Rezzonics/SuperFuzzWah/Simulation/FuzzWah_LTSpice_sch.jpg

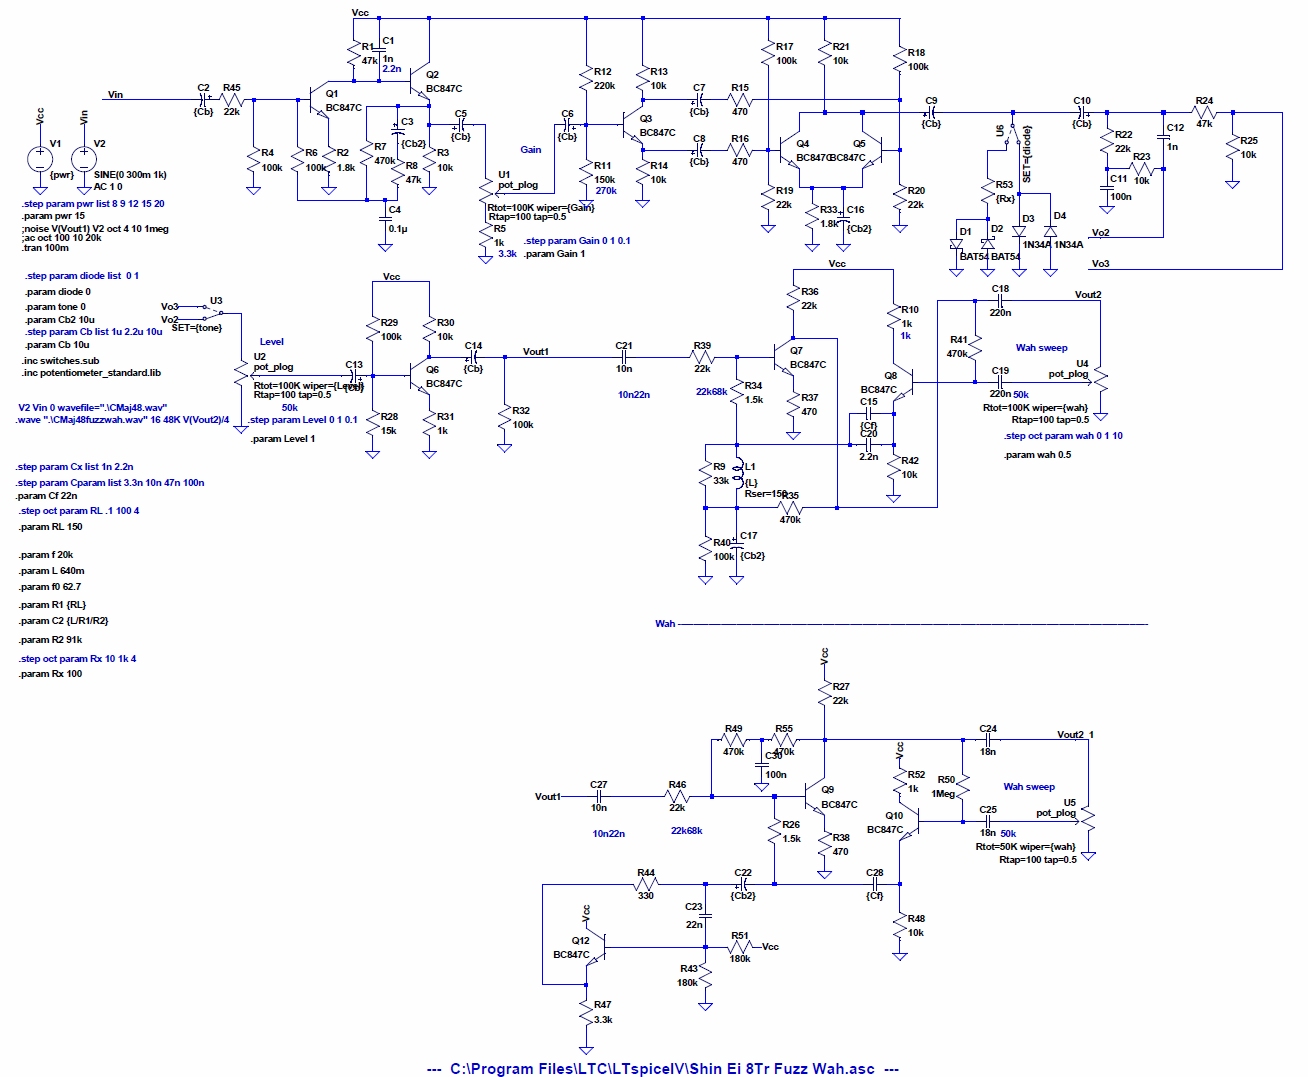
Simulation/FuzzWah_LTSpice_sch.jpg
