Rezzonics/SuperFuzzWah/Simulation/FuzzWah_LTSpice_V2.jpg

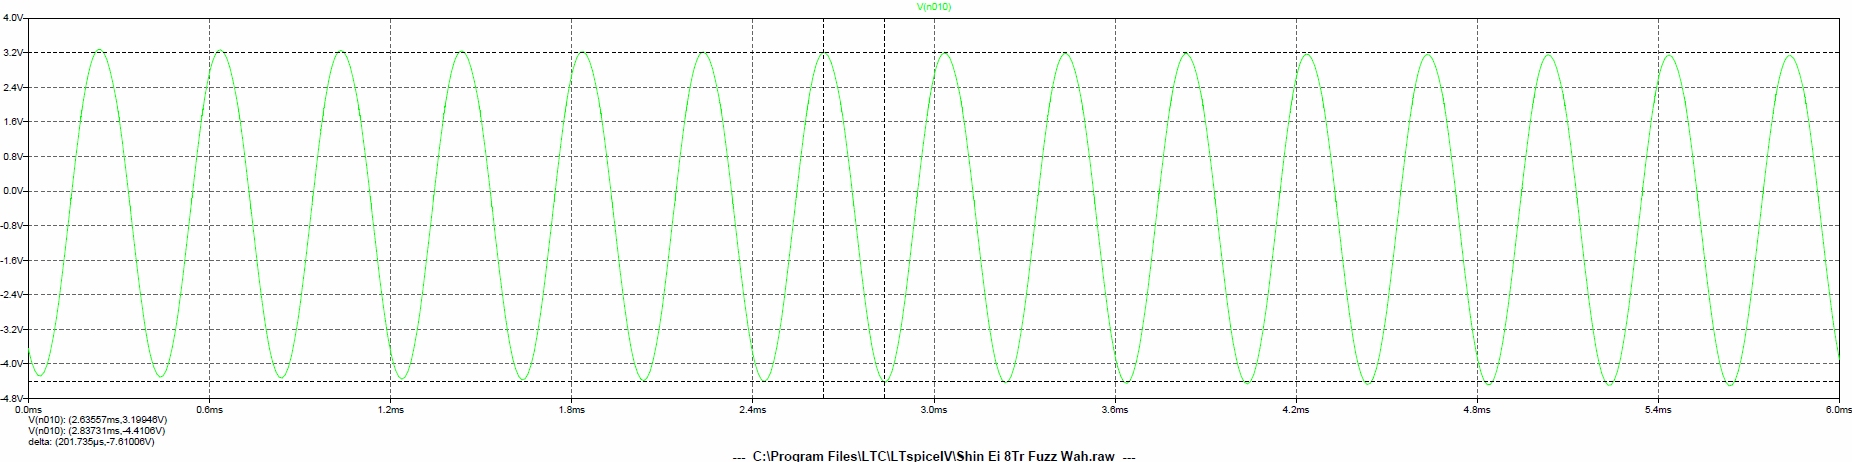
Simulation/FuzzWah_LTSpice_V2.jpg
