Rezzonics/SuperFuzzWah/Simulation/FuzzWah_LTSpice_V3.jpg

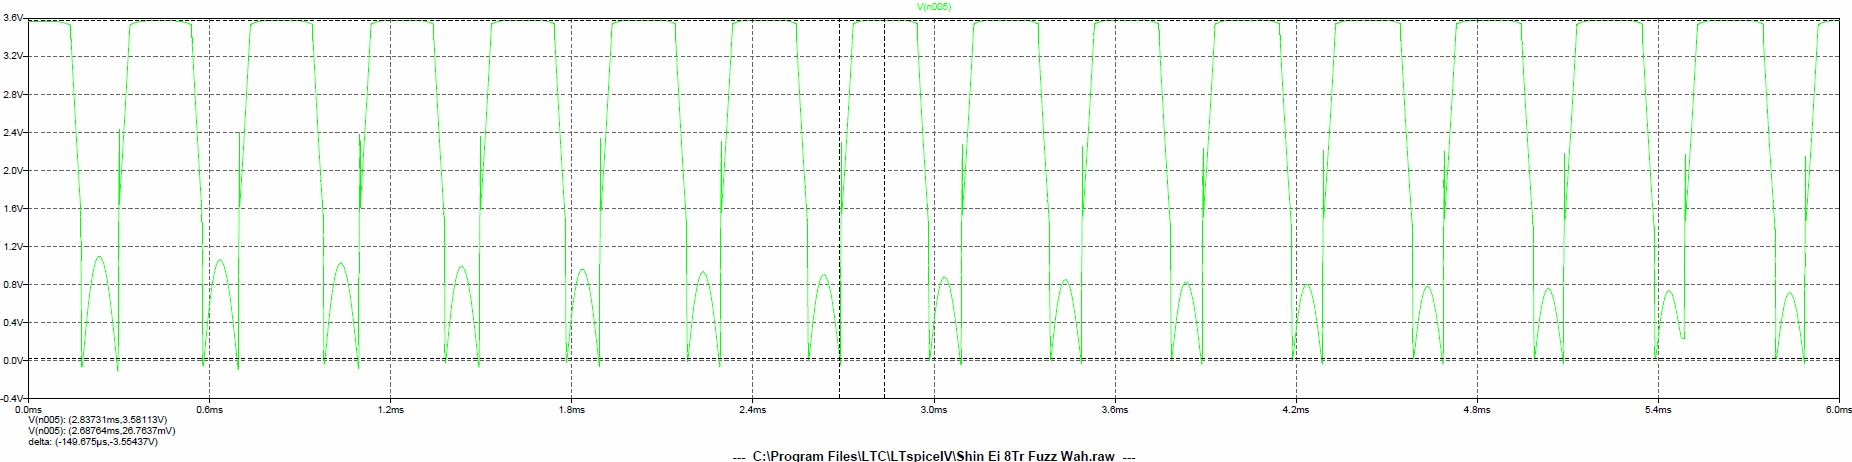
Simulation/FuzzWah_LTSpice_V3.jpg
