Rezzonics/SuperFuzzWah/Simulation/FuzzWah_LTSpice_V4.jpg

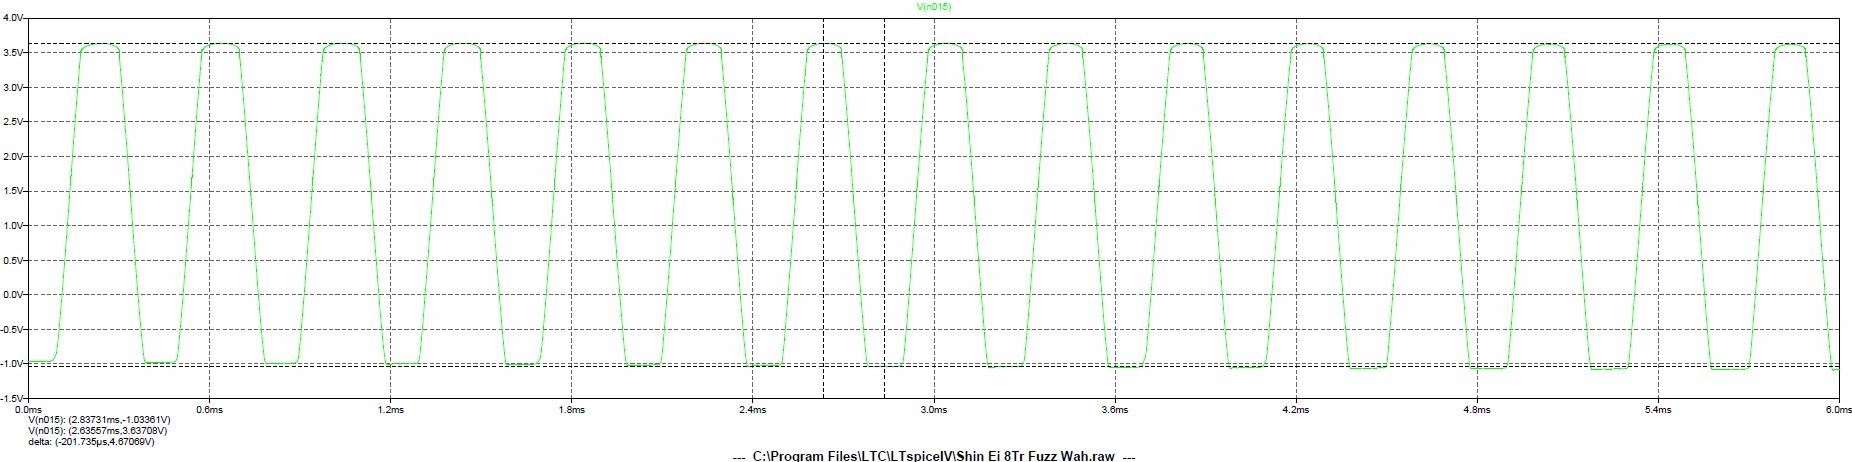
Simulation/FuzzWah_LTSpice_V4.jpg
