Rezzonics/SuperFuzzWah/Simulation/FuzzWah_LTSpice_V5.jpg

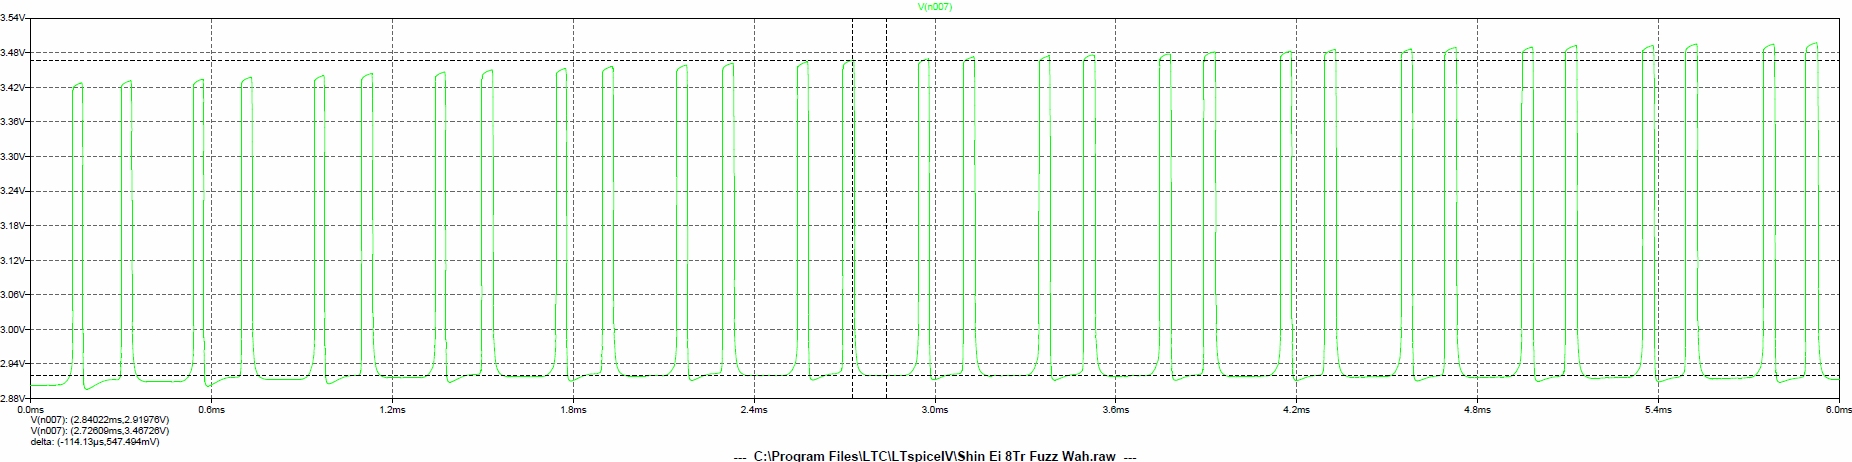
Simulation/FuzzWah_LTSpice_V5.jpg
