Rezzonics/SuperFuzzWah/Simulation/FuzzWah_LTSpice_V8.jpg

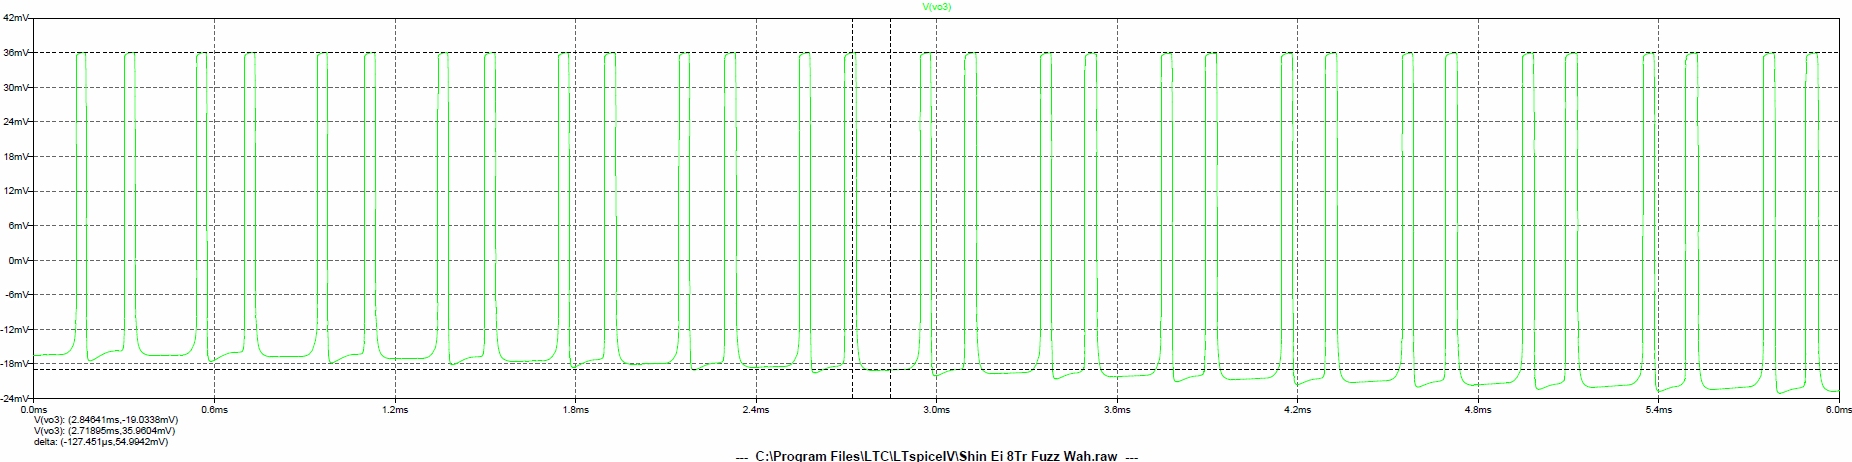
Simulation/FuzzWah_LTSpice_V8.jpg
