Rezzonics/SuperFuzzWah/Simulation/FuzzWah_LTSpice_V9.jpg

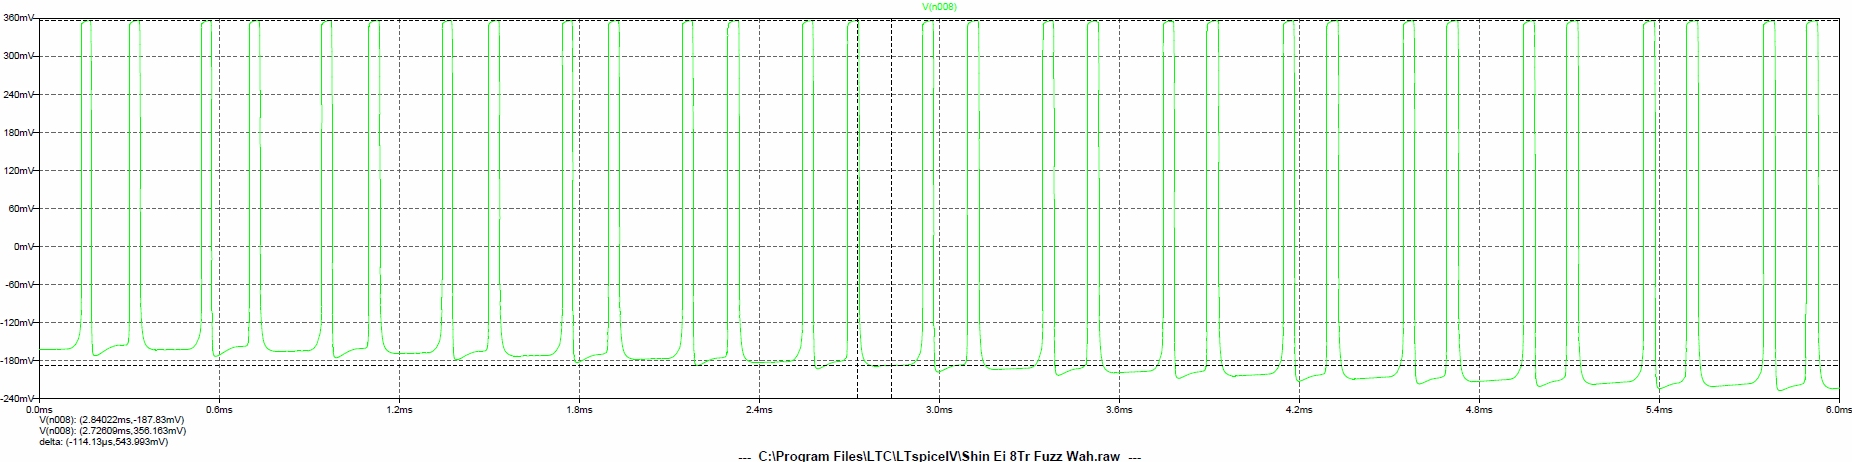
Simulation/FuzzWah_LTSpice_V9.jpg
