Rezzonics/SuperFuzzWah/Simulation/FuzzWah_LTSpice_V12_1.jpg

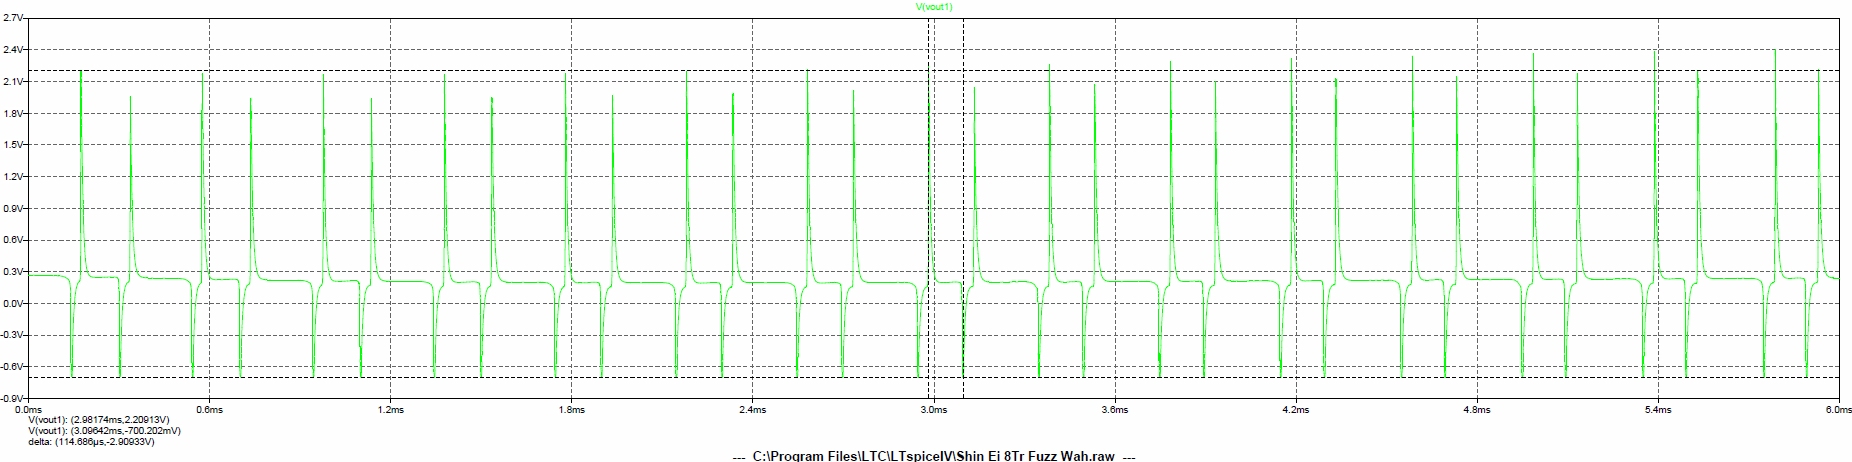
Simulation/FuzzWah_LTSpice_V12_1.jpg
