Rezzonics/SuperFuzzWah/Simulation/FuzzWah_LTSpice_V13.jpg

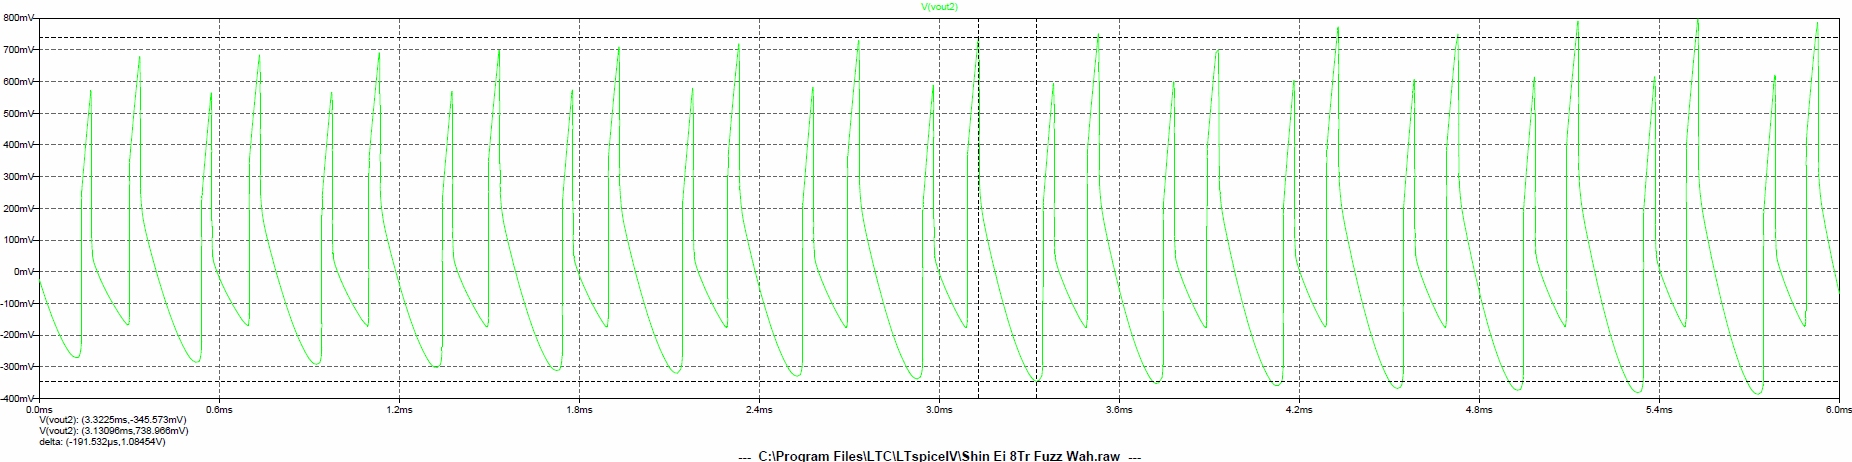
Simulation/FuzzWah_LTSpice_V13.jpg
