Rezzonics/SuperFuzzWah/SuperFuzzWah/SuperFuzzWah_1.1.sch.pdf

A

A

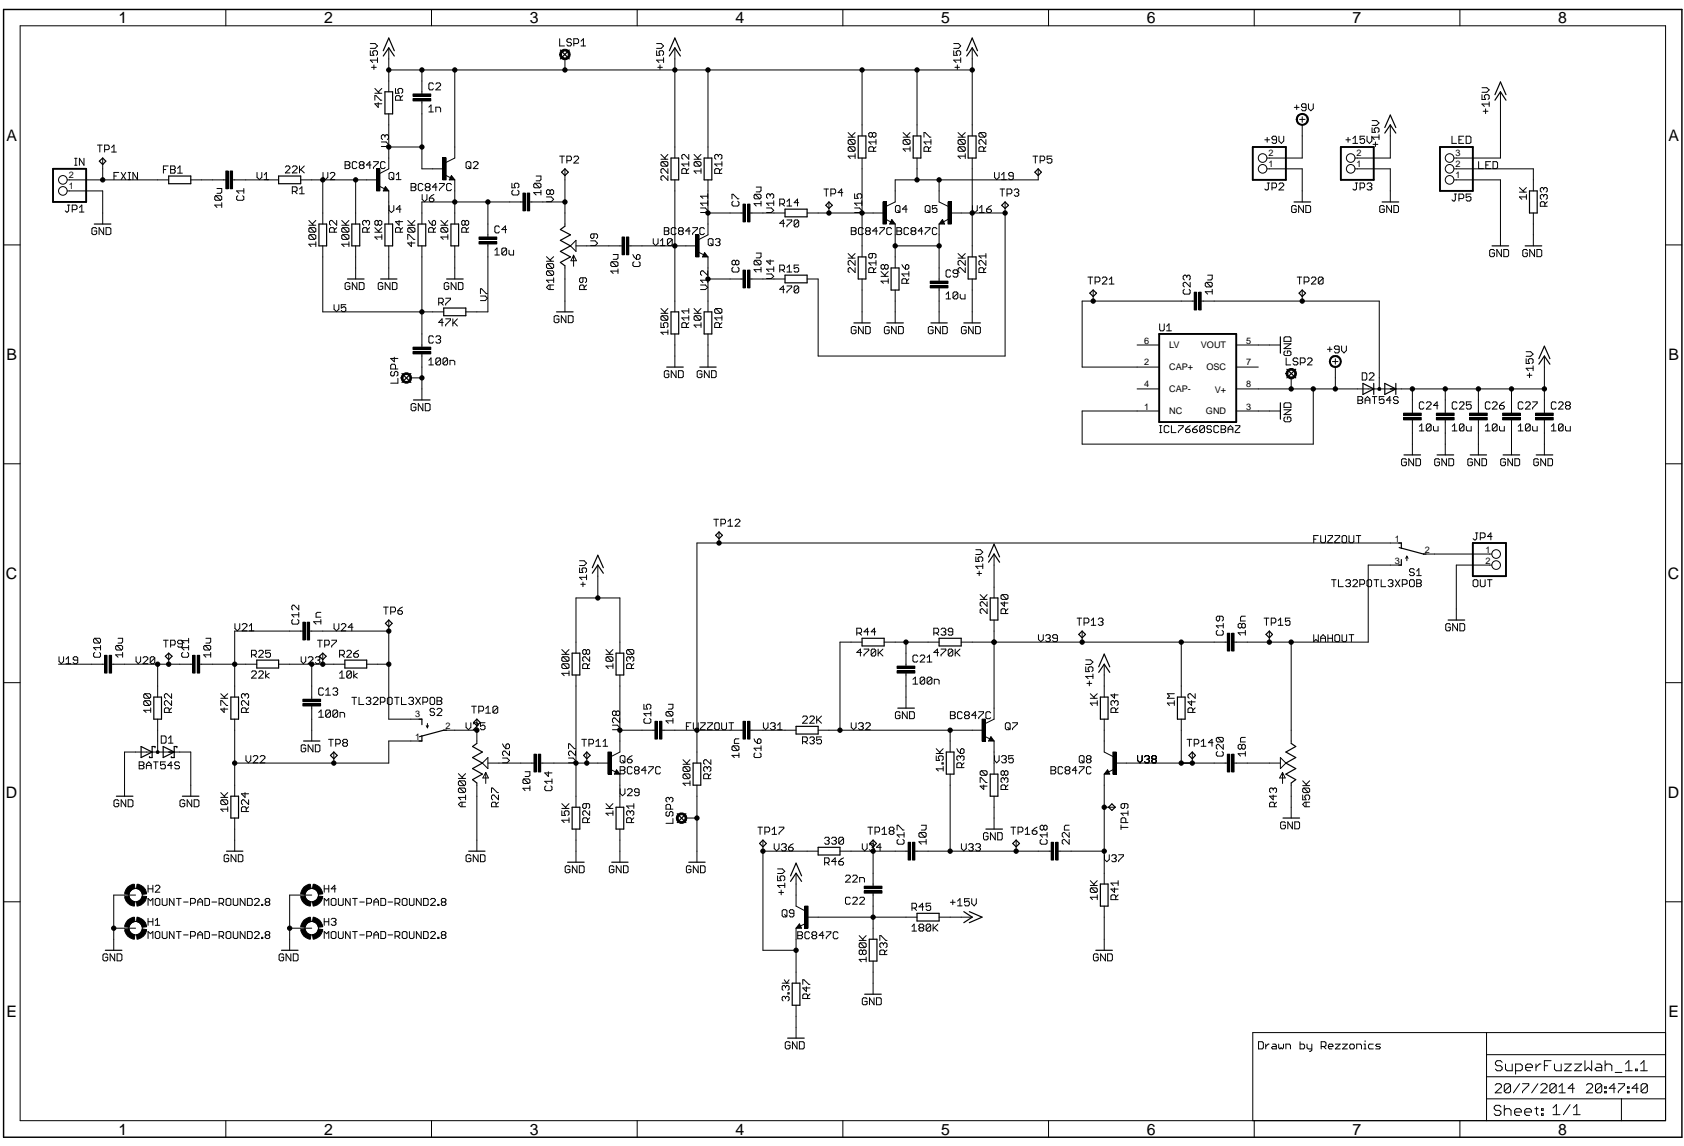
[picture p24: page 1]
CAP-; VOUT; GND; OSC; 7 CAP+
