Rezzonics/SuperFuzzWah/Simulation/Shin Ei 8Tr Fuzz Wah.rawV132.pdf

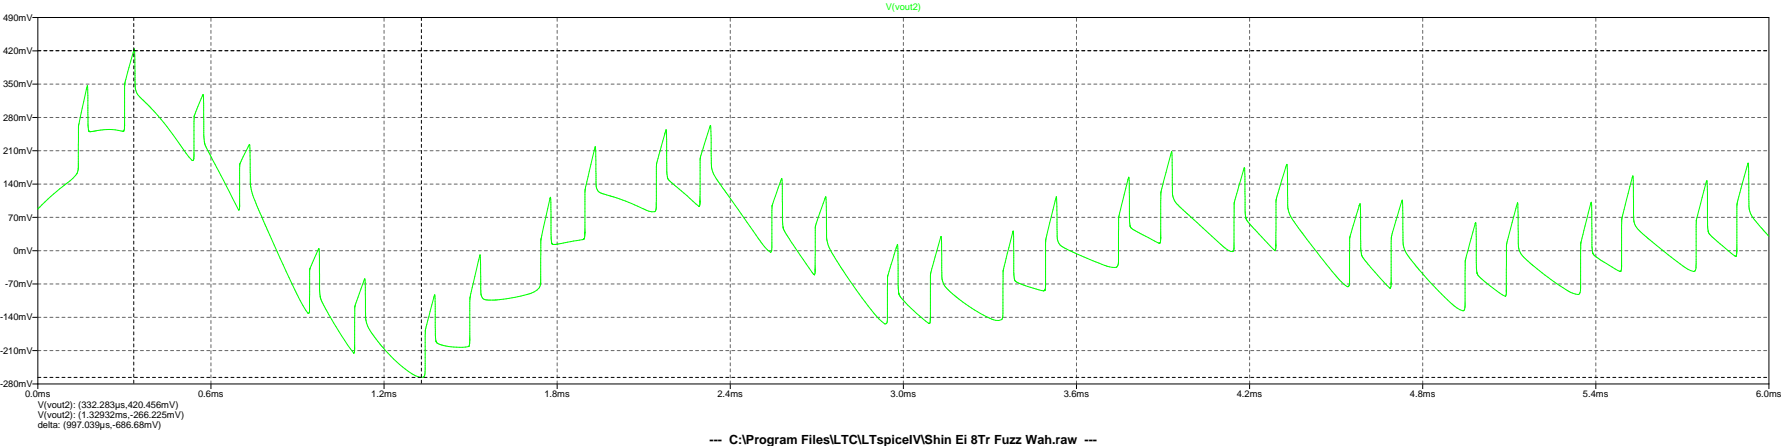
[picture p29: page 1]
V(vout2); V(vout2): (332.283µs,420.456mV) V(vout2): (1.32932ms,-266.225mV) delta: (997.039µs,-686.68mV)

--- C:\Program Files\LTC\LTspiceIV\Shin Ei 8Tr Fuzz Wah.raw ---
