Rezzonics/SuperFuzzWah/Simulation/Shin Ei 8Tr Fuzz Wah.rawV3.pdf

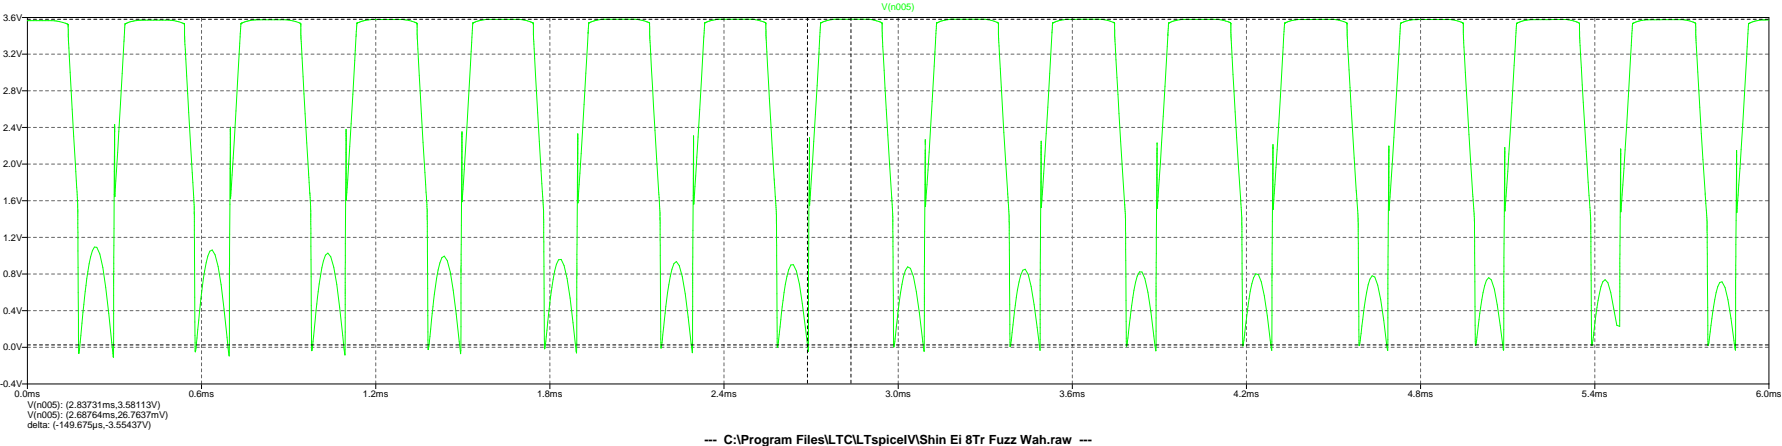
[picture p30: page 1]
V(n005): (2.83731ms,3.58113V) V(n005): (2.68764ms,26.7637mV) delta: (-149.675µs,-3.55437V)

--- C:\Program Files\LTC\LTspiceIV\Shin Ei 8Tr Fuzz Wah.raw ---
