Rezzonics/SuperFuzzWah/Simulation/Gyrator Wah.asc

C1: polcap; {Cb2}; V=25 Irms=39m Rser=2.8 Lser=0 mfg="Nichicon" pn="UPR1E100MAH" type="Al electrolytic"
C2: cap; 18n
C3: cap; 18n
C4: cap; 10n
C5: cap; {Cf}
C6: polcap; 10µ; V=25 Irms=39m Rser=2.8 Lser=0 mfg="Nichicon" pn="UPR1E100MAH" type="Al electrolytic"
C7: cap; 100n
C8: cap; 22n
C9: cap; 220n
C10: cap; 220n
C12: cap; 10n
C13: cap; 22n
L1: ind; 640m; Rser=150
Q1: npn; BC547C
Q2: npn; BC547C
Q3: npn; BC547C
Q4: npn; BC547C
Q5: npn; BC547C
R1: res; 1.5k
R2: res; 22k
R3: res; 470
R4: res; 22k
R5: res; 10k
R6: res; 470k
R7: res; 1Meg
R8: res; 1k
R9: res; 1.5k
R10: res; 22k
R11: res; 470k
R12: res; 180k
R13: res; 330
R14: res; 3.3k
R15: res; 180k
R16: res; 470
R17: res; 22k
R18: res; 100k
R19: res; 10k
R20: res; 470k
R21: res; 470k
R22: res; 33k
R23: res; 1k
U1: potentiometer_standard; Rtot=50K wiper={wah}; Rtap=100 tap=0.5
U2: potentiometer_standard; Rtot=100K wiper={wah}; Rtap=100 tap=0.5
V1: voltage; {pwr}
V2: voltage; SINE(0 1 300); AC 1 0
Named nets: Vin, 0, Vcc, Vout2_1, Vl1, Vout2
50k
Wah sweep
10n22n
22k68k
1k
.step oct param wah 0 1 10
50k
Wah sweep
.param wah 1
10n22n
22k68k
.step oct param Cx 1n 10u 4
.param Cf 22n
.step oct param RL 10 500 4
.param RL 150
.param L 1/(2*pi*f0)**2/Cb2
.param R1 {RL}
.param f 20k
.param C2 {L/R1/R2}
.param R2 91k
;tran 0 100m 80m
.ac oct 10 10 20k
;noise V(Vout1) V2 oct 4 10 1meg
.step param pwr list 8 9 12 15 20
.param pwr 15
.inc potentiometer_standard.lib
.param Cb2 10u
.param Cb 10u
.step oct param Rx 1k 10Meg 4
.param f0 63
Gyrator
