Rezzonics/SuperFuzzWah/Simulation/Shin Ei 8Tr Fuzz Wah1.asc

C1: cap; 1n
C2: polcap; {Cb}; V=10 Irms=0 Rser=2.5 Lser=0 mfg="AVX" pn="TAJC106M010" type="Tantalum"
C3: polcap; {Cb2}; V=25 Irms=39m Rser=2.8 Lser=0 mfg="Nichicon" pn="UPR1E100MAH" type="Al electrolytic"
C4: cap; 0.1µ
C5: polcap; {Cb}; V=10 Irms=0 Rser=2.5 Lser=0 mfg="AVX" pn="TAJC106M010" type="Tantalum"
C6: polcap; {Cb}; V=10 Irms=0 Rser=2.5 Lser=0 mfg="AVX" pn="TAJC106M010" type="Tantalum"
C7: polcap; {Cb}; V=25 Irms=39m Rser=2.8 Lser=0 mfg="Nichicon" pn="UPR1E100MAH" type="Al electrolytic"
C8: polcap; {Cb}; V=25 Irms=39m Rser=2.8 Lser=0 mfg="Nichicon" pn="UPR1E100MAH" type="Al electrolytic"
C9: polcap; {Cb}; V=10 Irms=0 Rser=2.5 Lser=0 mfg="AVX" pn="TAJC106M010" type="Tantalum"
C10: polcap; {Cb}; V=10 Irms=0 Rser=2.5 Lser=0 mfg="AVX" pn="TAJC106M010" type="Tantalum"
C11: cap; 100n
C12: cap; 1n
C13: polcap; {Cb}; V=16 Irms=0 Rser=2.8 Lser=0 mfg="AVX" pn="TAJC106M016" type="Tantalum"
C14: polcap; {Cb}; V=16 Irms=0 Rser=2.8 Lser=0 mfg="AVX" pn="TAJC106M016" type="Tantalum"
C15: cap; {Cf}
C16: polcap; {Cb2}; V=25 Irms=39m Rser=2.8 Lser=0 mfg="Nichicon" pn="UPR1E100MAH" type="Al electrolytic"
C17: polcap; {Cb2}; V=25 Irms=39m Rser=2.8 Lser=0 mfg="Nichicon" pn="UPR1E100MAH" type="Al electrolytic"
C18: cap; 220n
C19: cap; 220n
C20: cap; 2.2n
C21: cap; 10n
C22: polcap; {Cb2}; V=25 Irms=39m Rser=2.8 Lser=0 mfg="Nichicon" pn="UPR1E100MAH" type="Al electrolytic"
C23: cap; 22n
C24: cap; 18n
C25: cap; 18n
C26: cap; 10µ; V=25 Irms=0 Rser=0.001 Lser=0 mfg="TDK" pn="C575OX7RIE106M" type="X7R"
C27: cap; 10n
C28: cap; {Cf}
C30: cap; 100n
C31: cap; 10µ; V=25 Irms=0 Rser=0.001 Lser=0 mfg="TDK" pn="C575OX7RIE106M" type="X7R"
C32: cap; 10µ; V=25 Irms=0 Rser=0.001 Lser=0 mfg="TDK" pn="C575OX7RIE106M" type="X7R"
C33: cap; 10µ; V=25 Irms=0 Rser=0.001 Lser=0 mfg="TDK" pn="C575OX7RIE106M" type="X7R"
C34: cap; 10µ; V=25 Irms=0 Rser=0.001 Lser=0 mfg="TDK" pn="C575OX7RIE106M" type="X7R"
C35: cap; 10µ; V=25 Irms=0 Rser=0.001 Lser=0 mfg="TDK" pn="C575OX7RIE106M" type="X7R"
D1: schottky; BAT54
D2: schottky; BAT54
D3: diode; 1N34A
D4: diode; 1N34A
D5: schottky; BAT54
D6: schottky; BAT54
L1: ind; {L}; Rser=150
L2: FerriteBead; 431n; Ipk=0.5 Rser=0.065 Rpar=144 Cpar=3.2f mfg="Wurth Elektronik" pn="742 792 02"
Q1: npn; BC847C
Q2: npn; BC847C
Q3: npn; BC847C
Q4: npn; BC847C
Q5: npn; BC847C
Q6: npn; BC847C
Q7: npn; BC847C
Q8: npn; BC847C
Q9: npn; BC847C
Q10: npn; BC847C
Q12: npn; BC847C
R1: res; 47k
R2: res; 1.8k
R3: res; 10k
R4: res; 100k
R5: res; 1k
R6: res; 100k
R7: res; 470k
R8: res; 47k
R9: res; 33k
R10: res; 1k
R11: res; 150k
R12: res; 220k
R13: res; 10k
R14: res; 10k
R15: res; 470
R16: res; 470
R17: res; 100k
R18: res; 100k
R19: res; 22k
R20: res; 22k
R21: res; 10k
R22: res; 22k
R23: res; 10k
R24: res; 47k
R25: res; 10k
R26: res; 1.5k
R27: res; 22k
R28: res; 15k
R29: res; 100k
R30: res; 10k
R31: res; 1k
R32: res; 100k
R33: res; 1.8k
R34: res; 1.5k
R35: res; 470k
R36: res; 22k
R37: res; 470
R38: res; 470
R39: res; 22k
R40: res; 100k
R41: res; 470k
R42: res; 10k
R43: res; 180k
R44: res; 330
R45: res; 22k
R46: res; 22k
R47: res; 3.3k
R48: res; 10k
R49: res; 470k
R50: res; 1Meg
R51: res; 180k
R52: res; 1k
R53: res; {Rx}
R55: res; 470k
U1: potentiometer_standard; Rtot=100K wiper={Gain}; Rtap=100 tap=0.5
U2: potentiometer_standard; Rtot=100K wiper={Level}; Rtap=100 tap=0.5
U3: spdt; SET={tone}
U4: potentiometer_standard; Rtot=100K wiper={wah}; Rtap=100 tap=0.5
U5: potentiometer_standard; Rtot=50K wiper={wah}; Rtap=100 tap=0.5
U6: spdt; SET={diode}
U7: LTC1044
V1: voltage; {pwr}
V2: voltage; SINE(0 300m 2.5k); AC 1 0
V3: voltage; {pwr/2}
Named nets: 0, Vcc, Vin, Vo3, Vo2, Vout1, Vout2, Vout2_1, Vcc_2, Vcc_3
.tran 100m
.step param Gain 0 1 0.1
.step param Level 0 1 0.1
Wah ---------------------------------------------------------------------------------------------------------------------------------------------------------
;ac oct 100 10 20k
;noise V(Vout1) V2 oct 4 10 1meg
.wave ".\\CMaj48fuzzwah.wav" 16 48K V(Vout2)/4
V2 Vin 0 wavefile=".\\CMaj48.wav"
270k
2.2n
.inc potentiometer_standard.lib
.inc switches.sub
.param tone 0
.step param Cparam list 3.3n 10n 47n 100n
.param Cf 22n
1k
.step oct param wah 0 1 10
3.3k
50k
Gain
Level
Wah sweep
.param Cb2 10u
.step param Cb list 1u 2.2u 10u
50k
.param wah 0.5
.step param pwr list 8 9 12 15 20
.param pwr 16
10n22n
22k68k
.param Level 1
.param Gain 1
.step oct param RL .1 100 4
.param RL 150
.param L 640m
.param f0 62.7
.param R1 {RL}
.param f 20k
.param C2 {L/R1/R2}
.param R2 91k
50k
Wah sweep
10n22n
22k68k
.step oct param Rx 10 1k 4
.param diode 0
.param Rx 100
.step param diode list  0 1
.step param Cx list 1n 2.2n
.param Cb 10u
